xp5-org/ntsc-framebuffer/ltspice_sim/video_output_amplifier.asc

D1: diode
D2: diode
M1: nmos; 2N7002
M2: nmos; 2N7002
M3: nmos; 2N7002
Q1: pnp; 2N5087
R1: res; 60R
R2: res; 180R
R3: res; 150R
R4: res; 600R
R5: res; 150R
R6: res; 150R
R7: res; 800R
R8: res; 330R
R9: res; 1200R
R10: res; 15R
R11: res; 600R
R12: res; 2400R
R13: res; 800R
R16: res; 75R
R17: res; 1K
R18: res; 150R
V1: voltage; 5
V2: voltage; SINE(0 5 3580000)
Named nets: 0, video_output, mosfet_output, colorburst
.tran 0 .000003s 0s .00000001s
